mend0z0/E-Stationer/Hardware/_Sub_HW_EPaper/v1_20231122/Released Folder/vX.Y - YYYYMMDD/3D/3D View Pic/_HW_EPaper_Bottom.png

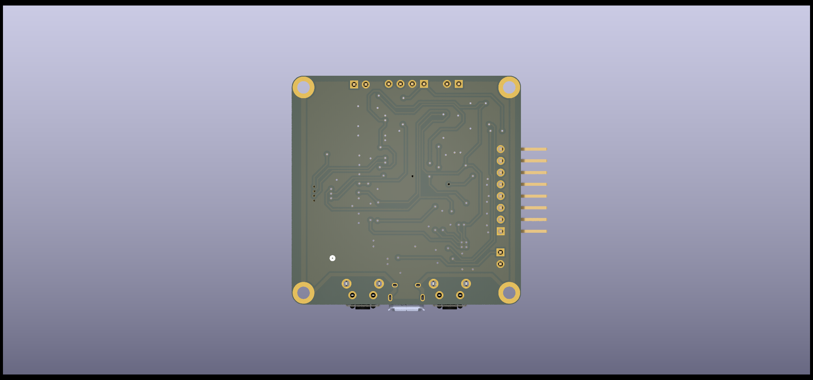
Hardware/_Sub_HW_EPaper/v1_20231122/Released Folder/vX.Y - YYYYMMDD/3D/3D View Pic/_HW_EPaper_Bottom.png
