mend0z0/E-Stationer/Hardware/_Sub_HW_EPen/v1_20231122/Design Folder/Design Guides/Function Table for the SN74HCS365.png

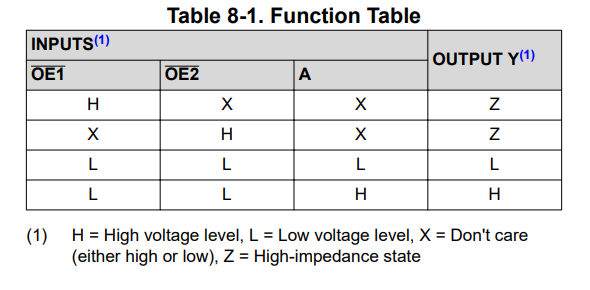
Hardware/_Sub_HW_EPen/v1_20231122/Design Folder/Design Guides/Function Table for the SN74HCS365.png
